S-March/smarchGlasses_Public/Firmware/smarchGlasses/src/user_peripheral.c

/**
 ****************************************************************************************
 *
 * @file user_peripheral.c
 *
 * @brief Peripheral project source code.
 *
 * Copyright (C) 2015-2019 Dialog Semiconductor.
 * This computer program includes Confidential, Proprietary Information
 * of Dialog Semiconductor. All Rights Reserved.
 *
 ****************************************************************************************
 */

/**
 ****************************************************************************************
 * @addtogroup APP
 * @{
 ****************************************************************************************
 */

/*
 * INCLUDE FILES
 ****************************************************************************************
 */

#include "rwip_config.h"             // SW configuration
#include "gap.h"
#include "app_easy_timer.h"
#include "user_peripheral.h"
#include "user_periph_setup.h"
#include "user_custs1_impl.h"
#include "user_custs1_def.h"
#include "co_bt.h"
#include "rf_531.h"
#include "user_io_expander_driver.h"

/*
 * TYPE DEFINITIONS
 ****************************************************************************************
 */

// Manufacturer Specific Data ADV structure type
struct mnf_specific_data_ad_structure
{
    uint8_t ad_structure_size;
    uint8_t ad_structure_type;
    uint8_t company_id[APP_AD_MSD_COMPANY_ID_LEN];
    uint8_t proprietary_data[APP_AD_MSD_DATA_LEN];
};

/*
 * GLOBAL VARIABLE DEFINITIONS
 ****************************************************************************************
 */

uint8_t app_connection_idx                      __SECTION_ZERO("retention_mem_area0");
timer_hnd app_adv_data_update_timer_used        __SECTION_ZERO("retention_mem_area0");
timer_hnd app_param_update_request_timer_used   __SECTION_ZERO("retention_mem_area0");

// Retained variables
struct mnf_specific_data_ad_structure mnf_data  __SECTION_ZERO("retention_mem_area0"); //@RETENTION MEMORY
// Index of manufacturer data in advertising data or scan response data (when MSB is 1)
uint8_t mnf_data_index                          __SECTION_ZERO("retention_mem_area0"); //@RETENTION MEMORY
uint8_t stored_adv_data_len                     __SECTION_ZERO("retention_mem_area0"); //@RETENTION MEMORY
uint8_t stored_scan_rsp_data_len                __SECTION_ZERO("retention_mem_area0"); //@RETENTION MEMORY
uint8_t stored_adv_data[ADV_DATA_LEN]           __SECTION_ZERO("retention_mem_area0"); //@RETENTION MEMORY
uint8_t stored_scan_rsp_data[SCAN_RSP_DATA_LEN] __SECTION_ZERO("retention_mem_area0"); //@RETENTION MEMORY

extern uint16_t ledOnTime;

/*
 * FUNCTION DEFINITIONS
 ****************************************************************************************
*/

/**
 ****************************************************************************************
 * @brief Initialize Manufacturer Specific Data
 ****************************************************************************************
 */
static void mnf_data_init()
{
    mnf_data.ad_structure_size = sizeof(struct mnf_specific_data_ad_structure ) - sizeof(uint8_t); // minus the size of the ad_structure_size field
    mnf_data.ad_structure_type = GAP_AD_TYPE_MANU_SPECIFIC_DATA;
    mnf_data.company_id[0] = APP_AD_MSD_COMPANY_ID & 0xFF; // LSB
    mnf_data.company_id[1] = (APP_AD_MSD_COMPANY_ID >> 8 )& 0xFF; // MSB
    mnf_data.proprietary_data[0] = 0;
    mnf_data.proprietary_data[1] = 0;
}

/**
 ****************************************************************************************
 * @brief Update Manufacturer Specific Data
 ****************************************************************************************
 */
static void mnf_data_update()
{
    uint16_t data;

    data = mnf_data.proprietary_data[0] | (mnf_data.proprietary_data[1] << 8);
    data += 1;
    mnf_data.proprietary_data[0] = data & 0xFF;
    mnf_data.proprietary_data[1] = (data >> 8) & 0xFF;

    if (data == 0xFFFF) {
         mnf_data.proprietary_data[0] = 0;
         mnf_data.proprietary_data[1] = 0;
    }
}

/**
 ****************************************************************************************
 * @brief Add an AD structure in the Advertising or Scan Response Data of the
 *        GAPM_START_ADVERTISE_CMD parameter struct.
 * @param[in] cmd               GAPM_START_ADVERTISE_CMD parameter struct
 * @param[in] ad_struct_data    AD structure buffer
 * @param[in] ad_struct_len     AD structure length
 * @param[in] adv_connectable   Connectable advertising event or not. It controls whether
 *                              the advertising data use the full 31 bytes length or only
 *                              28 bytes (Document CCSv6 - Part 1.3 Flags).
 ****************************************************************************************
 */
static void app_add_ad_struct(struct gapm_start_advertise_cmd *cmd, void *ad_struct_data, uint8_t ad_struct_len, uint8_t adv_connectable)
{
    uint8_t adv_data_max_size = (adv_connectable) ? (ADV_DATA_LEN - 3) : (ADV_DATA_LEN);

    if ((adv_data_max_size - cmd->info.host.adv_data_len) >= ad_struct_len)
    {
        // Append manufacturer data to advertising data
        memcpy(&cmd->info.host.adv_data[cmd->info.host.adv_data_len], ad_struct_data, ad_struct_len);

        // Update Advertising Data Length
        cmd->info.host.adv_data_len += ad_struct_len;

        // Store index of manufacturer data which are included in the advertising data
        mnf_data_index = cmd->info.host.adv_data_len - sizeof(struct mnf_specific_data_ad_structure);
    }
    else if ((SCAN_RSP_DATA_LEN - cmd->info.host.scan_rsp_data_len) >= ad_struct_len)
    {
        // Append manufacturer data to scan response data
        memcpy(&cmd->info.host.scan_rsp_data[cmd->info.host.scan_rsp_data_len], ad_struct_data, ad_struct_len);

        // Update Scan Response Data Length
        cmd->info.host.scan_rsp_data_len += ad_struct_len;

        // Store index of manufacturer data which are included in the scan response data
        mnf_data_index = cmd->info.host.scan_rsp_data_len - sizeof(struct mnf_specific_data_ad_structure);
        // Mark that manufacturer data is in scan response and not advertising data
        mnf_data_index |= 0x80;
    }
    else
    {
        // Manufacturer Specific Data do not fit in either Advertising Data or Scan Response Data
        ASSERT_WARNING(0);
    }
    // Store advertising data length
    stored_adv_data_len = cmd->info.host.adv_data_len;
    // Store advertising data
    memcpy(stored_adv_data, cmd->info.host.adv_data, stored_adv_data_len);
    // Store scan response data length
    stored_scan_rsp_data_len = cmd->info.host.scan_rsp_data_len;
    // Store scan_response data
    memcpy(stored_scan_rsp_data, cmd->info.host.scan_rsp_data, stored_scan_rsp_data_len);
}

/**
 ****************************************************************************************
 * @brief Advertisement data update timer callback function.
 ****************************************************************************************
*/
static void adv_data_update_timer_cb()
{
    // If mnd_data_index has MSB set, manufacturer data is stored in scan response
    uint8_t *mnf_data_storage = (mnf_data_index & 0x80) ? stored_scan_rsp_data : stored_adv_data;

    // Update manufacturer data
    mnf_data_update();

    // Update the selected fields of the advertising data (manufacturer data)
    memcpy(mnf_data_storage + (mnf_data_index & 0x7F), &mnf_data, sizeof(struct mnf_specific_data_ad_structure));

    // Update advertising data on the fly
    app_easy_gap_update_adv_data(stored_adv_data, stored_adv_data_len, stored_scan_rsp_data, stored_scan_rsp_data_len);

    // Restart timer for the next advertising update
    app_adv_data_update_timer_used = app_easy_timer(APP_ADV_DATA_UPDATE_TO, adv_data_update_timer_cb);
}

/**
 ****************************************************************************************
 * @brief Parameter update request timer callback function.
 ****************************************************************************************
*/
static void param_update_request_timer_cb()
{
    app_easy_gap_param_update_start(app_connection_idx);
    app_param_update_request_timer_used = EASY_TIMER_INVALID_TIMER;
}

void user_app_init(void)
{
    app_param_update_request_timer_used = EASY_TIMER_INVALID_TIMER;

    // Initialize Manufacturer Specific Data
    mnf_data_init();

    // Initialize Advertising and Scan Response Data
    memcpy(stored_adv_data, USER_ADVERTISE_DATA, USER_ADVERTISE_DATA_LEN);
    stored_adv_data_len = USER_ADVERTISE_DATA_LEN;
    memcpy(stored_scan_rsp_data, USER_ADVERTISE_SCAN_RESPONSE_DATA, USER_ADVERTISE_SCAN_RESPONSE_DATA_LEN);
    stored_scan_rsp_data_len = USER_ADVERTISE_SCAN_RESPONSE_DATA_LEN;
	
#if (USING_DEV_KIT)
    GPIO_SetInactive(GPIO_LED_PORT, GPIO_LED_PIN);
#else
		i2c_ioExpander_initialize();
#endif
	
    default_app_on_init();
		ledOnTime = LED_ON_TIME;
}

void user_app_adv_start(void)
{
		/**************************************/
		/***********SMARCH ADDITION************/
		/***Raise TX power to up to +2.5 dbm***/
		rf_pa_pwr_set(RF_TX_PWR_LVL_PLUS_2d5);
		set_recommended_settings();
		/**************************************/
	
    // Schedule the next advertising data update
    app_adv_data_update_timer_used = app_easy_timer(APP_ADV_DATA_UPDATE_TO, adv_data_update_timer_cb);

    struct gapm_start_advertise_cmd* cmd;
    cmd = app_easy_gap_undirected_advertise_get_active();

    // Add manufacturer data to initial advertising or scan response data, if there is enough space
    app_add_ad_struct(cmd, &mnf_data, sizeof(struct mnf_specific_data_ad_structure), 1);

    app_easy_gap_undirected_advertise_start();
}

void user_app_connection(uint8_t connection_idx, struct gapc_connection_req_ind const *param)
{
    if (app_env[connection_idx].conidx != GAP_INVALID_CONIDX)
    {
				/**************************************/
				/***********SMARCH ADDITION************/
				/*Lower TX power back to normal levels*/
				rf_pa_pwr_set(RF_TX_PWR_LVL_PLUS_2d5);
				set_recommended_settings();
        app_connection_idx = connection_idx;
				/**************************************/

        // Stop the advertising data update timer
        app_easy_timer_cancel(app_adv_data_update_timer_used);

        // Check if the parameters of the established connection are the preferred ones.
        // If not then schedule a connection parameter update request.
        if ((param->con_interval < user_connection_param_conf.intv_min) ||
            (param->con_interval > user_connection_param_conf.intv_max) ||
            (param->con_latency != user_connection_param_conf.latency) ||
            (param->sup_to != user_connection_param_conf.time_out))
        {
            // Connection params are not these that we expect
            app_param_update_request_timer_used = app_easy_timer(APP_PARAM_UPDATE_REQUEST_TO, param_update_request_timer_cb);
        }
    }
    else
    {
        // No connection has been established, restart advertising
        user_app_adv_start();
    }

    default_app_on_connection(connection_idx, param);
}

void user_app_adv_undirect_complete(uint8_t status)
{
    // If advertising was canceled then update advertising data and start advertising again
    if (status == GAP_ERR_CANCELED)
    {
        user_app_adv_start();
    }
}

void user_app_disconnect(struct gapc_disconnect_ind const *param)
{
    // Cancel the parameter update request timer
    if (app_param_update_request_timer_used != EASY_TIMER_INVALID_TIMER)
    {
        app_easy_timer_cancel(app_param_update_request_timer_used);
        app_param_update_request_timer_used = EASY_TIMER_INVALID_TIMER;
    }
    // Update manufacturer data for the next advertsing event
    mnf_data_update();
    // Restart Advertising
    user_app_adv_start();
}

void user_catch_rest_hndl(ke_msg_id_t const msgid,
                          void const *param,
                          ke_task_id_t const dest_id,
                          ke_task_id_t const src_id)
{
    switch(msgid)
    {
        case CUSTS1_VAL_WRITE_IND:
        {
            struct custs1_val_write_ind const *msg_param = (struct custs1_val_write_ind const *)(param);

            switch (msg_param->handle)
            {
                case SVC1_IDX_LED_STATE_VAL:
                    user_svc1_led_wr_ind_handler(msgid, msg_param, dest_id, src_id);
                    break;
                case SVC1_IDX_LED_TIME_VAL:
                    user_svc1_led_time_wr_ind_handler(msgid, msg_param, dest_id, src_id);
                    break;

                default:
                    break;
            }
        } break;

        case GAPC_PARAM_UPDATED_IND:
        {
            // Cast the "param" pointer to the appropriate message structure
            struct gapc_param_updated_ind const *msg_param = (struct gapc_param_updated_ind const *)(param);

            // Check if updated Conn Params filled to preferred ones
            if ((msg_param->con_interval >= user_connection_param_conf.intv_min) &&
                (msg_param->con_interval <= user_connection_param_conf.intv_max) &&
                (msg_param->con_latency == user_connection_param_conf.latency) &&
                (msg_param->sup_to == user_connection_param_conf.time_out))
            {
            }
        } break;

        default:
            break;
    }
}

/// @} APP
