S-March/smarchGlasses_Public/Firmware/smarchGlasses/src/user_peripheral.h

/**
 ****************************************************************************************
 *
 * @file user_peripheral_proj.h
 *
 * @brief Peripheral project header file.
 *
 * Copyright (C) 2015-2019 Dialog Semiconductor.
 * This computer program includes Confidential, Proprietary Information
 * of Dialog Semiconductor. All Rights Reserved.
 *
 ****************************************************************************************
 */

#ifndef _USER_PERIPHERAL_H_
#define _USER_PERIPHERAL_H_

/**
 ****************************************************************************************
 * @addtogroup APP
 * @ingroup RICOW
 *
 * @brief
 *
 * @{
 ****************************************************************************************
 */

/*
 * INCLUDE FILES
 ****************************************************************************************
 */

#include "rwble_config.h"
#include "app_task.h"                  // application task
#include "gapc_task.h"                 // gap functions and messages
#include "gapm_task.h"                 // gap functions and messages
#include "app.h"                       // application definitions
#include "co_error.h"                  // error code definitions
#include "arch_wdg.h"

#include "app_callback.h"
#include "app_default_handlers.h"


/*
 * DEFINES
 ****************************************************************************************
 */

/* Duration of timer for connection parameter update request */
#define APP_PARAM_UPDATE_REQUEST_TO         (1000)   // 1000*10ms = 10sec, The maximum allowed value is 41943sec (4194300 * 10ms)

/* Advertising data update timer */
#define APP_ADV_DATA_UPDATE_TO              (3000)   // 3000*10ms = 30sec, The maximum allowed value is 41943sec (4194300 * 10ms)

/* Manufacturer specific data constants */
#define APP_AD_MSD_COMPANY_ID       (0xABCD)
#define APP_AD_MSD_COMPANY_ID_LEN   (2)
#define APP_AD_MSD_DATA_LEN         (sizeof(uint16_t))

#define APP_PERIPHERAL_CTRL_TIMER_DELAY 100

/*
 * TYPE DEFINITIONS
 ****************************************************************************************
 */

/*
 * FUNCTION DECLARATIONS
 ****************************************************************************************
 */

/**
 ****************************************************************************************
 * @brief Application initialization function.
 ****************************************************************************************
*/
void user_app_init(void);

/**
 ****************************************************************************************
 * @brief Advertising function.
 ****************************************************************************************
*/
void user_app_adv_start(void);

/**
 ****************************************************************************************
 * @brief Connection function.
 * @param[in] connection_idx Connection Id index
 * @param[in] param Pointer to GAPC_CONNECTION_REQ_IND message
 ****************************************************************************************
*/
void user_app_connection(uint8_t connection_idx, 
                         struct gapc_connection_req_ind const *param);

/**
 ****************************************************************************************
 * @brief Undirect advertising completion function.
 * @param[in] status Command complete event message status
 ****************************************************************************************
*/
void user_app_adv_undirect_complete(uint8_t status);

/**
 ****************************************************************************************
 * @brief Disconnection function.
 * @param[in] param Pointer to GAPC_DISCONNECT_IND message
 ****************************************************************************************
*/
void user_app_disconnect(struct gapc_disconnect_ind const *param);

/**
 ****************************************************************************************
 * @brief Handles the messages that are not handled by the SDK internal mechanisms.
 * @param[in] msgid   Id of the message received.
 * @param[in] param   Pointer to the parameters of the message.
 * @param[in] dest_id ID of the receiving task instance.
 * @param[in] src_id  ID of the sending task instance.
 ****************************************************************************************
*/
void user_catch_rest_hndl(ke_msg_id_t const msgid,
                          void const *param,
                          ke_task_id_t const dest_id,
                          ke_task_id_t const src_id);

/// @} APP

#endif // _USER_PERIPHERAL_H_
